reif-is-a-foofie/Ezra/ezra_golden_phone/renders/emotional_recovery_warmth.png

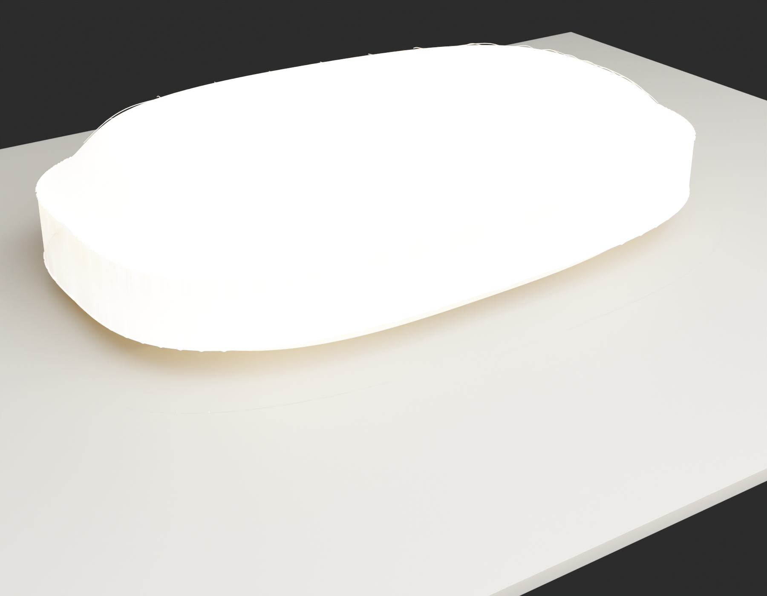
ezra_golden_phone/renders/emotional_recovery_warmth.png
