reif-is-a-foofie/Ezra/ezra_golden_phone/renders/hero_internal_glow.png

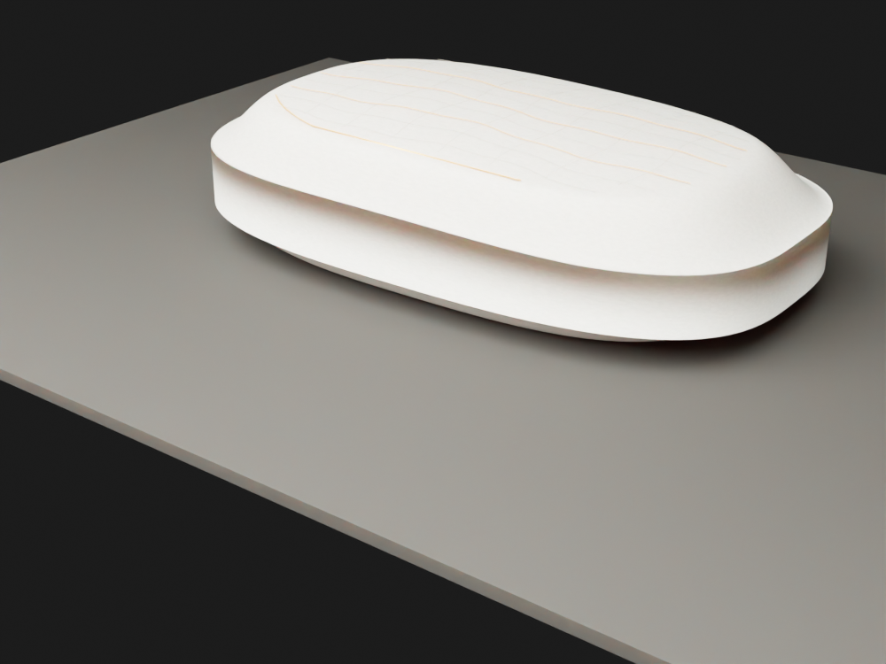
ezra_golden_phone/renders/hero_internal_glow.png
