reif-is-a-foofie/Ezra/ezra_nautilus/turntable/frame_000.png

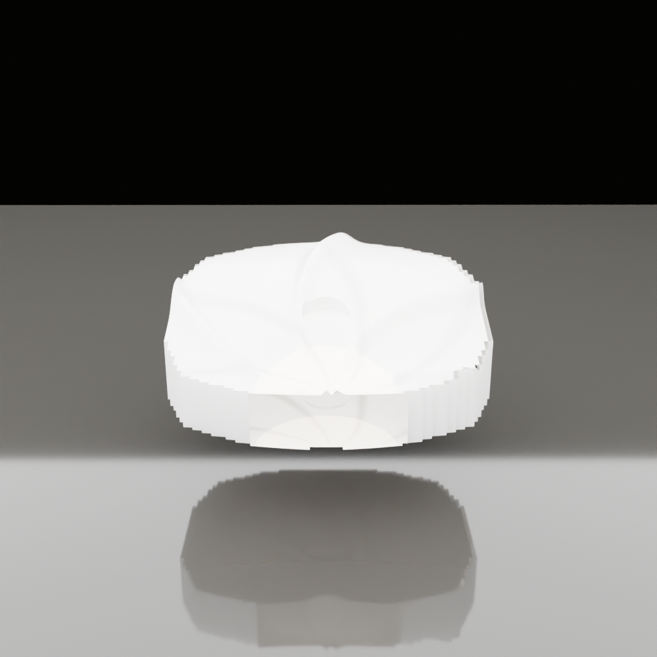
ezra_nautilus/turntable/frame_000.png
